nuniesmith/seed-holder/pictures/IMG_0148.JPEG

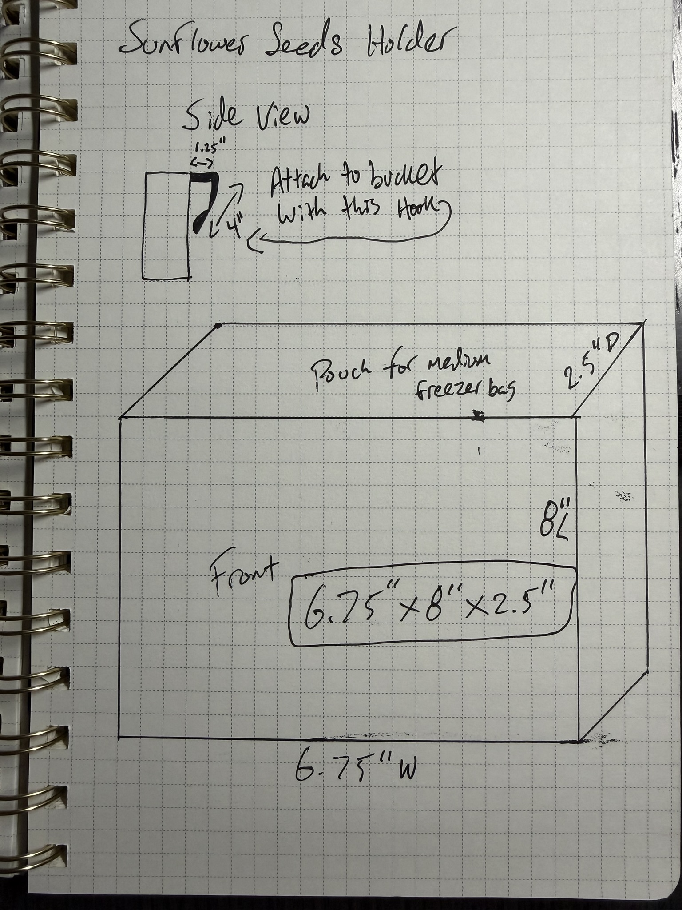
pictures/IMG_0148.JPEG
